apfelaudio/tiliqua/gateware/src/top/bootloader/fw/src/main.rs

#![no_std]
#![no_main]

use critical_section::Mutex;
use core::convert::TryInto;
use log::info;
use riscv_rt::entry;
use irq::handler;
use core::cell::RefCell;

use tiliqua_pac as pac;
use tiliqua_hal as hal;
use tiliqua_lib::*;
use tiliqua_lib::opt::*;
use tiliqua_lib::generated_constants::*;
use tiliqua_fw::*;
use tiliqua_lib::palette::ColorPalette;

use embedded_graphics::{
    mono_font::{ascii::FONT_9X15, ascii::FONT_9X15_BOLD, MonoTextStyle},
    pixelcolor::{Gray8, GrayColor},
    prelude::*,
    primitives::{PrimitiveStyleBuilder, Line},
    text::{Alignment, Text},
};

use opts::Options;
use hal::pca9635::Pca9635Driver;
use crate::manifest::Bitstream;

impl_ui!(UI,
         Options,
         Encoder0,
         Pca9635Driver<I2c0>,
         EurorackPmod0);

hal::impl_dma_display!(DMADisplay, H_ACTIVE, V_ACTIVE,
                       VIDEO_ROTATE_90);

pub const TIMER0_ISR_PERIOD_MS: u32 = 5;

struct App {
    ui: UI,
    reboot_n: Option<usize>,
    time_since_reboot_requested: u32,
}

impl App {
    pub fn new(opts: Options) -> Self {
        let peripherals = unsafe { pac::Peripherals::steal() };
        let encoder = Encoder0::new(peripherals.ENCODER0);
        let i2cdev = I2c0::new(peripherals.I2C0);
        let pca9635 = Pca9635Driver::new(i2cdev);
        let pmod = EurorackPmod0::new(peripherals.PMOD0_PERIPH);
        Self {
            ui: UI::new(opts, TIMER0_ISR_PERIOD_MS,
                        encoder, pca9635, pmod),
            reboot_n: None,
            time_since_reboot_requested: 0u32,
        }
    }
}

fn print_rebooting<D>(d: &mut D, rng: &mut fastrand::Rng)
where
    D: DrawTarget<Color = Gray8>,
{
    let style = MonoTextStyle::new(&FONT_9X15_BOLD, Gray8::WHITE);
    Text::with_alignment(
        "REBOOTING",
        Point::new(rng.i32(0..H_ACTIVE as i32), rng.i32(0..V_ACTIVE as i32)),
        style,
        Alignment::Center,
    )
    .draw(d).ok();
}

fn draw_summary<D>(d: &mut D, bitstream: &Bitstream, or: i32, ot: i32, hue: u8)
where
    D: DrawTarget<Color = Gray8>,
{
    let norm = MonoTextStyle::new(&FONT_9X15,      Gray8::new(0xB0 + hue));
    Text::with_alignment(
        "video:".into(),
        Point::new((H_ACTIVE/2 - 10) as i32 + or, (V_ACTIVE/2+20) as i32 + ot),
        norm,
        Alignment::Right,
    )
    .draw(d).ok();
    Text::with_alignment(
        &bitstream.video,
        Point::new((H_ACTIVE/2) as i32 + or, (V_ACTIVE/2+20) as i32 + ot),
        norm,
        Alignment::Left,
    )
    .draw(d).ok();
    Text::with_alignment(
        "brief:".into(),
        Point::new((H_ACTIVE/2 - 10) as i32 + or, (V_ACTIVE/2+40) as i32 + ot),
        norm,
        Alignment::Right,
    )
    .draw(d).ok();
    Text::with_alignment(
        &bitstream.brief,
        Point::new((H_ACTIVE/2) as i32 + or, (V_ACTIVE/2+40) as i32 + ot),
        norm,
        Alignment::Left,
    )
    .draw(d).ok();
}

fn timer0_handler(app: &Mutex<RefCell<App>>) {

    critical_section::with(|cs| {

        let mut app = app.borrow_ref_mut(cs);

        //
        // Update UI and options
        //

        app.ui.update();

        if app.ui.opts.modify() {
            if let Some(n) = app.ui.opts.view().selected() {
                app.reboot_n = Some(n)
            }
        }

        if let Some(n) = app.reboot_n {
            app.time_since_reboot_requested += app.ui.period_ms;
            // Give codec time to mute and display time to draw 'REBOOTING'
            if app.time_since_reboot_requested > 500 {
                info!("BITSTREAM{}\n\r", n);
            }
        }
    });
}

pub fn write_palette(video: &mut Video0, p: palette::ColorPalette) {
    for i in 0..PX_INTENSITY_MAX {
        for h in 0..PX_HUE_MAX {
            let rgb = palette::compute_color(i, h, p);
            video.set_palette_rgb(i as u8, h as u8, rgb.r, rgb.g, rgb.b);
        }
    }
}

#[entry]
fn main() -> ! {
    let peripherals = pac::Peripherals::take().unwrap();
    let pmod = peripherals.PMOD0_PERIPH;

    let sysclk = pac::clock::sysclk();
    let serial = Serial0::new(peripherals.UART0);
    let mut timer = Timer0::new(peripherals.TIMER0, sysclk);
    let mut video = Video0::new(peripherals.VIDEO_PERIPH);

    crate::handlers::logger_init(serial);

    info!("Hello from Tiliqua bootloader!");

    let manifest = manifest::BitstreamManifest::find().unwrap_or(
        manifest::BitstreamManifest::unknown_manifest());

    info!("BitstreamManifest created with:");
    for bitstream in &manifest.bitstreams {
        info!("* Bitstream *");
        info!("- name '{}'",  bitstream.name);
        info!("- brief '{}'", bitstream.brief);
        info!("- video '{}'", bitstream.video);
    }

    let opts = opts::Options::new(&manifest);
    let app = Mutex::new(RefCell::new(App::new(opts)));

    handler!(timer0 = || timer0_handler(&app));

    irq::scope(|s| {

        s.register(handlers::Interrupt::TIMER0, timer0);

        timer.enable_tick_isr(TIMER0_ISR_PERIOD_MS,
                              pac::Interrupt::TIMER0);

        let mut logo_coord_ix = 0u32;
        let mut rng = fastrand::Rng::with_seed(0);
        let mut display = DMADisplay {
            framebuffer_base: PSRAM_FB_BASE as *mut u32,
        };
        video.set_persist(1024);

        let stroke = PrimitiveStyleBuilder::new()
            .stroke_color(Gray8::new(0xB0))
            .stroke_width(1)
            .build();

        write_palette(&mut video, ColorPalette::Linear);

        loop {

            let (opts, reboot_n) = critical_section::with(|cs| {
                (app.borrow_ref(cs).ui.opts.clone(),
                 app.borrow_ref(cs).reboot_n.clone())
            });

            draw::draw_options(&mut display, &opts, 100, V_ACTIVE/2-50, 0).ok();
            draw::draw_name(&mut display, H_ACTIVE/2, V_ACTIVE-50, 0, UI_NAME, UI_SHA).ok();

            if let Some(n) = opts.boot.selected {
                draw_summary(&mut display, &manifest.bitstreams[n], -20, -18, 0);
                Line::new(Point::new(255, (V_ACTIVE/2 - 55 + (n as u32)*18) as i32),
                          Point::new((H_ACTIVE/2-90) as i32, (V_ACTIVE/2+8) as i32))
                          .into_styled(stroke)
                          .draw(&mut display).ok();
            }

            for _ in 0..10 {
                let _ = draw::draw_boot_logo(&mut display,
                                             (H_ACTIVE/2) as i32,
                                             100 as i32,
                                             logo_coord_ix);
                logo_coord_ix += 1;
            }

            if let Some(_) = reboot_n {
                pmod.flags().write(|w|  w.mute().bit(true) );
                print_rebooting(&mut display, &mut rng);
            }
        }
    })
}
