apfelaudio/tiliqua/gateware/src/top/bootloader/fw/src/opts.rs

use tiliqua_lib::opt::*;
use tiliqua_lib::impl_option_view;
use tiliqua_lib::impl_option_page;

use heapless::String;

use core::str::FromStr;
use crate::manifest;

use strum_macros::{EnumIter, IntoStaticStr};

#[derive(Clone, Copy, PartialEq, EnumIter, IntoStaticStr)]
#[strum(serialize_all = "SCREAMING-KEBAB-CASE")]
pub enum Screen {
    Boot,
}

#[derive(Clone)]
pub struct BootOptions {
    pub selected: Option<usize>,
    pub bitstream0: NumOption<u8>,
    pub bitstream1: NumOption<u8>,
    pub bitstream2: NumOption<u8>,
    pub bitstream3: NumOption<u8>,
    pub bitstream4: NumOption<u8>,
    pub bitstream5: NumOption<u8>,
    pub bitstream6: NumOption<u8>,
    pub bitstream7: NumOption<u8>,
}

impl_option_view!(BootOptions,
                  bitstream0,
                  bitstream1,
                  bitstream2,
                  bitstream3,
                  bitstream4,
                  bitstream5,
                  bitstream6,
                  bitstream7);

#[derive(Clone)]
pub struct Options {
    pub modify: bool,
    pub draw:bool,
    pub screen: EnumOption<Screen>,

    pub boot: BootOptions,
}

impl_option_page!(Options,
                  (Screen::Boot, boot));

impl Options {
    pub fn new(manifest: &manifest::BitstreamManifest) -> Options {
        Options {
            modify: false,
            draw: true,
            screen: EnumOption {
                name: String::from_str("screen").unwrap(),
                value: Screen::Boot,
            },
            boot: BootOptions {
                selected: Some(0),
                bitstream0: NumOption{
                    name: manifest.bitstreams[0].name.clone(),
                    value: 0,
                    step: 0,
                    min: 0,
                    max: 8,
                },
                bitstream1: NumOption{
                    name: manifest.bitstreams[1].name.clone(),
                    value: 1,
                    step: 0,
                    min: 0,
                    max: 8,
                },
                bitstream2: NumOption{
                    name: manifest.bitstreams[2].name.clone(),
                    value: 2,
                    step: 0,
                    min: 0,
                    max: 8,
                },
                bitstream3: NumOption{
                    name: manifest.bitstreams[3].name.clone(),
                    value: 3,
                    step: 0,
                    min: 0,
                    max: 8,
                },
                bitstream4: NumOption{
                    name: manifest.bitstreams[4].name.clone(),
                    value: 4,
                    step: 0,
                    min: 0,
                    max: 8,
                },
                bitstream5: NumOption{
                    name: manifest.bitstreams[5].name.clone(),
                    value: 5,
                    step: 0,
                    min: 0,
                    max: 8,
                },
                bitstream6: NumOption{
                    name: manifest.bitstreams[6].name.clone(),
                    value: 6,
                    step: 0,
                    min: 0,
                    max: 8,
                },
                bitstream7: NumOption{
                    name: manifest.bitstreams[7].name.clone(),
                    value: 7,
                    step: 0,
                    min: 0,
                    max: 8,
                },
            },
        }
    }
}
