apfelaudio/tiliqua/gateware/tests/test_midi.py

# Copyright (c) 2024 Seb Holzapfel <me@sebholzapfel.com>
#
# SPDX-License-Identifier: CERN-OHL-S-2.0

import math
import sys
import unittest
from parameterized         import parameterized

from amaranth              import *
from amaranth.sim          import *
from amaranth.lib          import wiring
from tiliqua               import midi, test_util

from amaranth_soc          import csr
from amaranth_soc.csr      import wishbone


class MidiTests(unittest.TestCase):

    @parameterized.expand([
        ["trs", False], # 3-byte
        ["usb", True],  # 4-byte
    ])
    def test_midi_decode(self, name, is_usb):

        dut = midi.MidiDecode(usb=is_usb)

        async def testbench(ctx):
            ctx.set(dut.i.valid,   1)
            if is_usb:
                ctx.set(dut.i.payload, 0x00)
                await ctx.tick()
            ctx.set(dut.i.payload, 0x92)
            await ctx.tick()
            ctx.set(dut.i.payload, 0x48)
            await ctx.tick()
            ctx.set(dut.i.payload, 0x96)
            await ctx.tick()
            p = ctx.get(dut.o.payload)
            self.assertEqual(p.midi_type, midi.MessageType.NOTE_ON)
            self.assertEqual(p.midi_channel, 2)
            self.assertEqual(p.midi_payload.note_on.note, 0x48)
            self.assertEqual(p.midi_payload.note_on.velocity, 0x96)

        sim = Simulator(dut)
        sim.add_clock(1e-6)
        sim.add_testbench(testbench)
        with sim.write_vcd(vcd_file=open(f"test_midi_decode_{name}.vcd", "w")):
            sim.run()

    def test_midi_voice_tracker(self):

        dut = midi.MidiVoiceTracker()

        note_range = list(range(40, 48))

        async def stimulus_notes(ctx):
            """Send some MIDI NOTE_ON events."""
            for note in note_range:
                # FIXME: valid before ready in TBs EVERYWHERE!
                ctx.set(dut.i.valid, 1)
                ctx.set(dut.i.payload.midi_type, midi.MessageType.NOTE_ON)
                ctx.set(dut.i.payload.midi_channel, 1)
                ctx.set(dut.i.payload.midi_payload.note_on.note, note)
                ctx.set(dut.i.payload.midi_payload.note_on.velocity, 0x60)
                await ctx.tick().until(dut.i.ready)
                ctx.set(dut.i.valid, 0)
                await ctx.tick()

            await ctx.tick().repeat(50)

            for note in note_range:
                ctx.set(dut.i.valid, 1)
                ctx.set(dut.i.payload.midi_type, midi.MessageType.NOTE_OFF)
                ctx.set(dut.i.payload.midi_channel, 1)
                ctx.set(dut.i.payload.midi_payload.note_off.note, note)
                ctx.set(dut.i.payload.midi_payload.note_off.velocity, 0x30)
                await ctx.tick().until(dut.i.ready)
                ctx.set(dut.i.valid, 0)
                await ctx.tick()

        async def testbench(ctx):
            """Check that the NOTE_ON / OFF events correspond to voice slots."""
            for ticks in range(400):
                for n in range(dut.max_voices):
                    note_in_slot = ctx.get(dut.o[n].note)
                    vel_in_slot  = ctx.get(dut.o[n].velocity)
                    gate_in_slot = ctx.get(dut.o[n].gate)
                    print(f"{ticks} slot{n}: note={note_in_slot} vel={vel_in_slot} gate={gate_in_slot}")
                    if n < len(note_range):
                        if ticks > 180 and ticks < 200:
                            # Verify NOTE_ON events written to voice slots.
                            self.assertEqual(note_in_slot, note_range[n])
                            self.assertEqual(vel_in_slot,  0x60)
                            self.assertEqual(gate_in_slot, 1)
                        if ticks > 380:
                            # Verify NOTE_OFF events removed from voice slots.
                            self.assertEqual(note_in_slot, note_range[n])
                            self.assertEqual(gate_in_slot, 0)
                            if dut.zero_velocity_gate:
                                self.assertEqual(vel_in_slot,  0x0)
                            else:
                                self.assertEqual(vel_in_slot,  0x30)
                await ctx.tick()

        sim = Simulator(dut)
        sim.add_clock(1e-6)
        sim.add_process(stimulus_notes)
        sim.add_testbench(testbench)
        with sim.write_vcd(vcd_file=open("test_midi_voice_tracker.vcd", "w")):
            sim.run()
