apfelaudio/tiliqua/gateware/src/example_soc/fw/src/lib.rs

#![no_std]
#![no_main]

pub use tiliqua_pac as pac;
pub use tiliqua_hal as hal;

tiliqua_hal::impl_serial! {
    Serial0: pac::UART,
}

tiliqua_hal::impl_timer! {
    Timer0: pac::TIMER,
}

tiliqua_hal::impl_i2c! {
    I2c0: pac::I2C0,
}

pub mod log;
